m0nka/mcHF/mechanical/back/closer/1.png

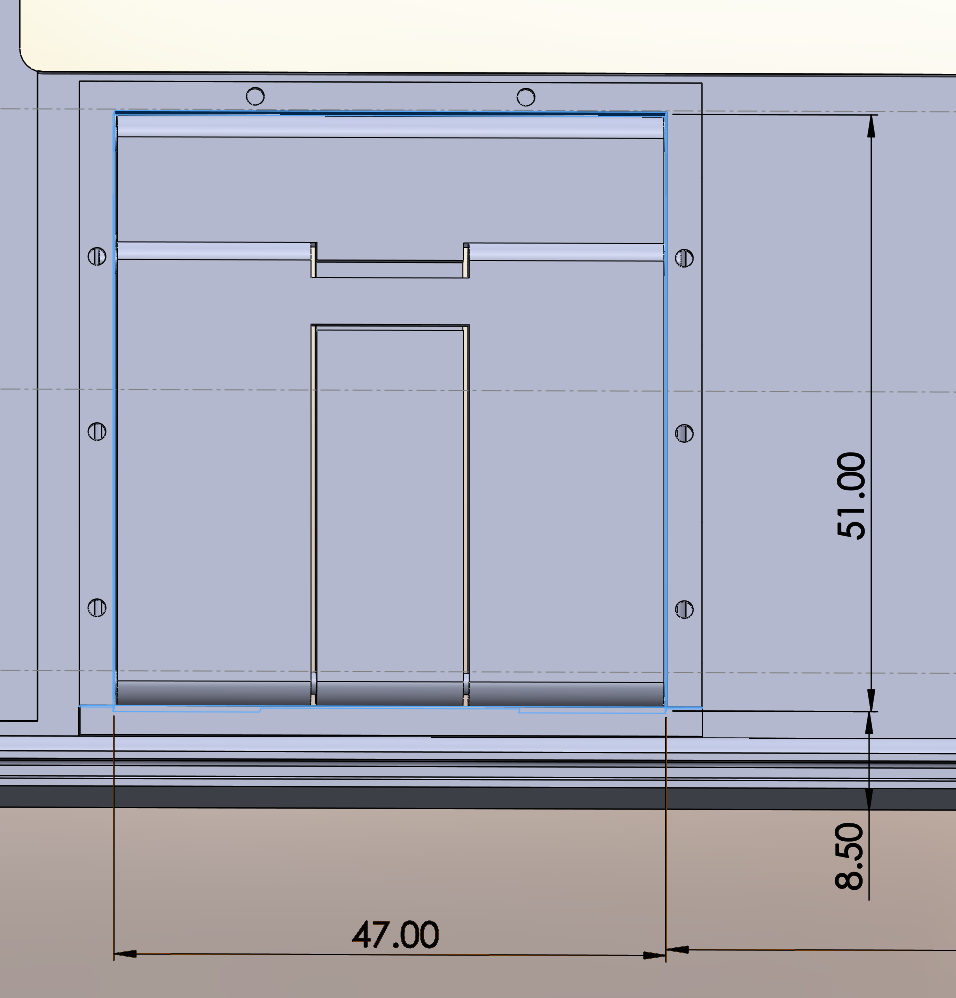
mechanical/back/closer/1.png
