m0nka/mcHF/mechanical/back/closer/2.png

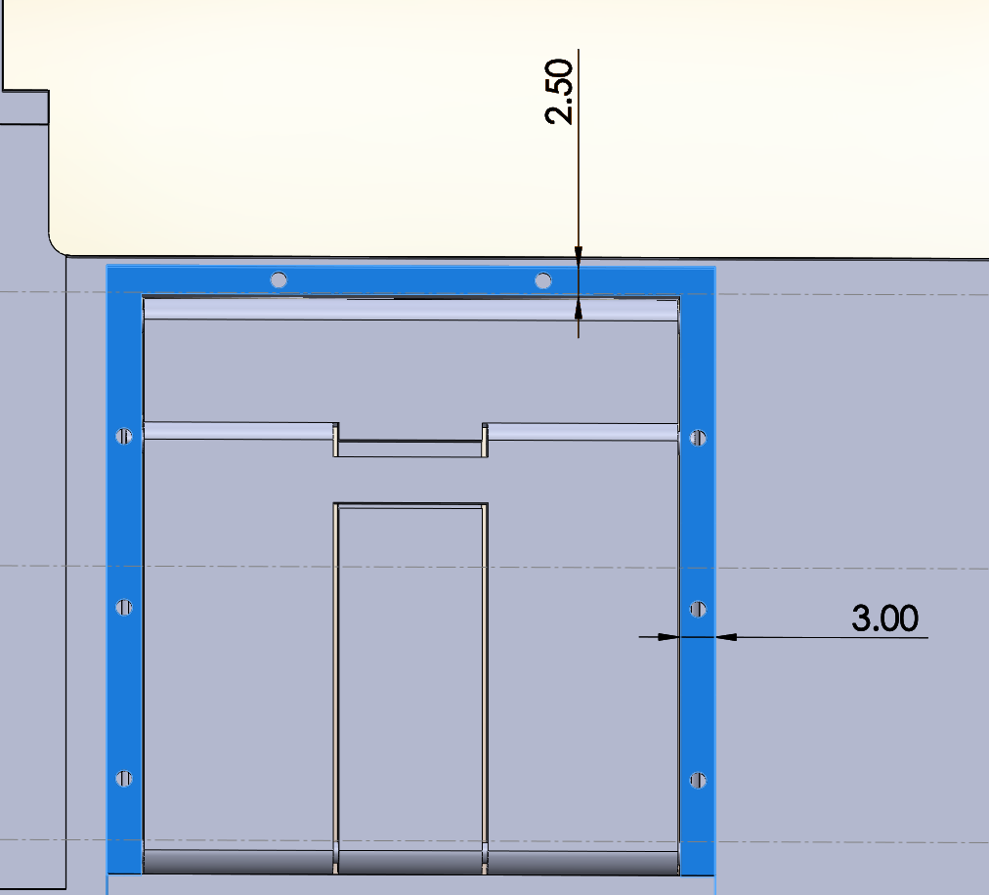
mechanical/back/closer/2.png
