m0nka/mcHF/mechanical/back/closer/3.png

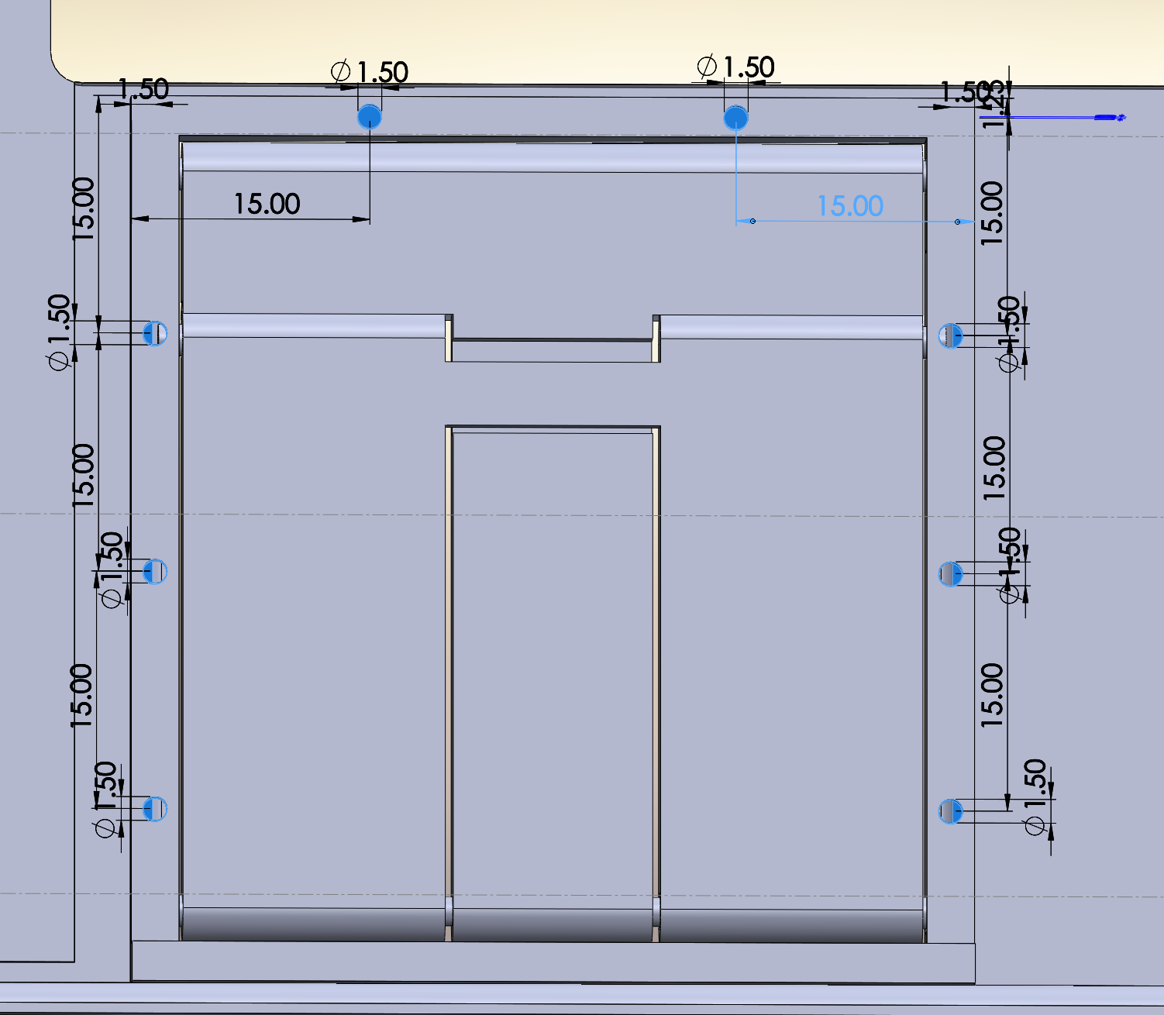
mechanical/back/closer/3.png
