m0nka/mcHF/mechanical/case/AK-C-C19/HTB1J9ANLXXXXXaTXXXXq6xXFXXXU.jpg

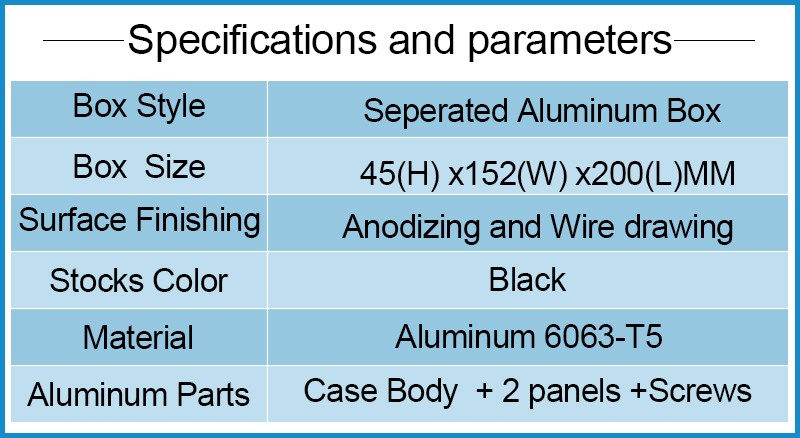
mechanical/case/AK-C-C19/HTB1J9ANLXXXXXaTXXXXq6xXFXXXU.jpg
