m0nka/mcHF/mechanical/case/AK-C-C19/HTB1t6IPLXXXXXXvXXXXq6xXFXXXi.jpg

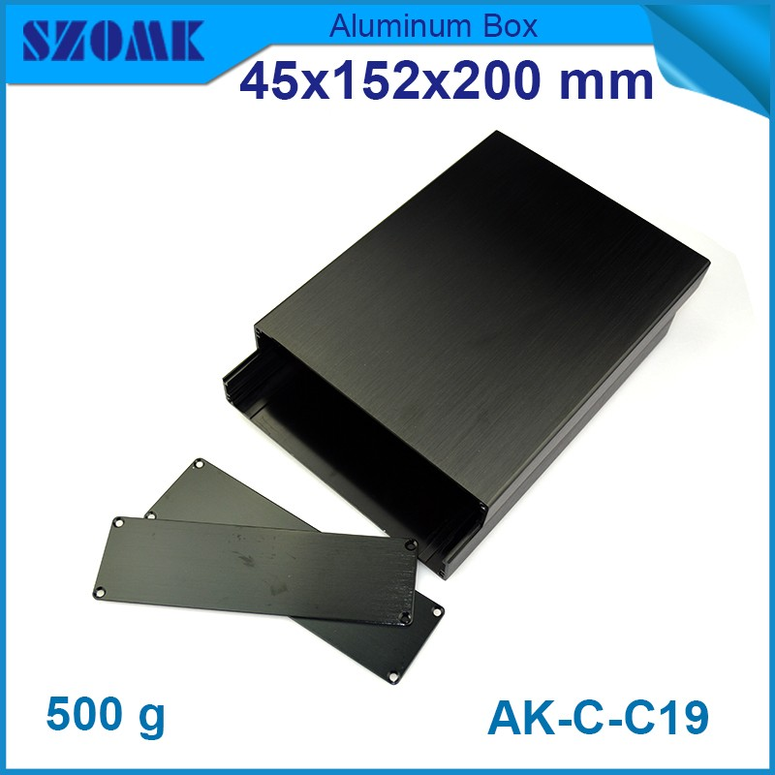
mechanical/case/AK-C-C19/HTB1t6IPLXXXXXXvXXXXq6xXFXXXi.jpg
