m0nka/mcHF/mechanical/case/AK-C-C19/HTB1tHIrLXXXXXaYXVXXq6xXFXXXV.jpg

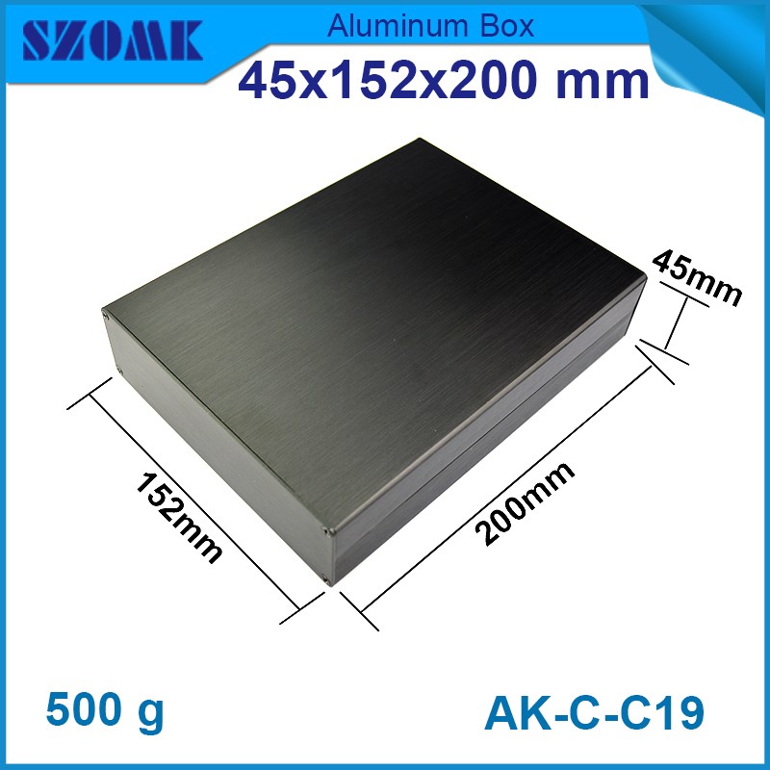
mechanical/case/AK-C-C19/HTB1tHIrLXXXXXaYXVXXq6xXFXXXV.jpg
