m0nka/mcHF/mechanical/case/AK-C-C19/HTB13bgQLXXXXXXDXXXXq6xXFXXXn.jpg

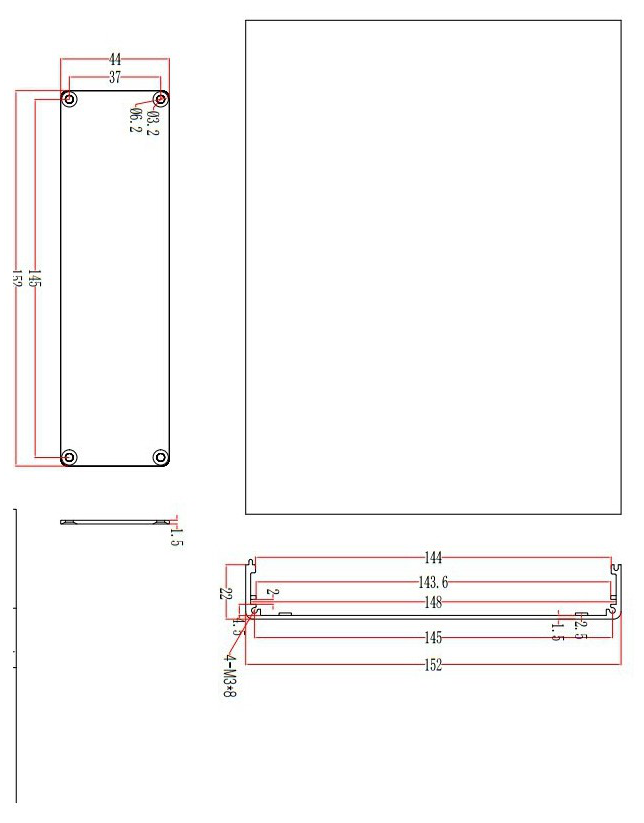
mechanical/case/AK-C-C19/HTB13bgQLXXXXXXDXXXXq6xXFXXXn.jpg
