m0nka/mcHF/testing/gerbers/0_8_5/1.png

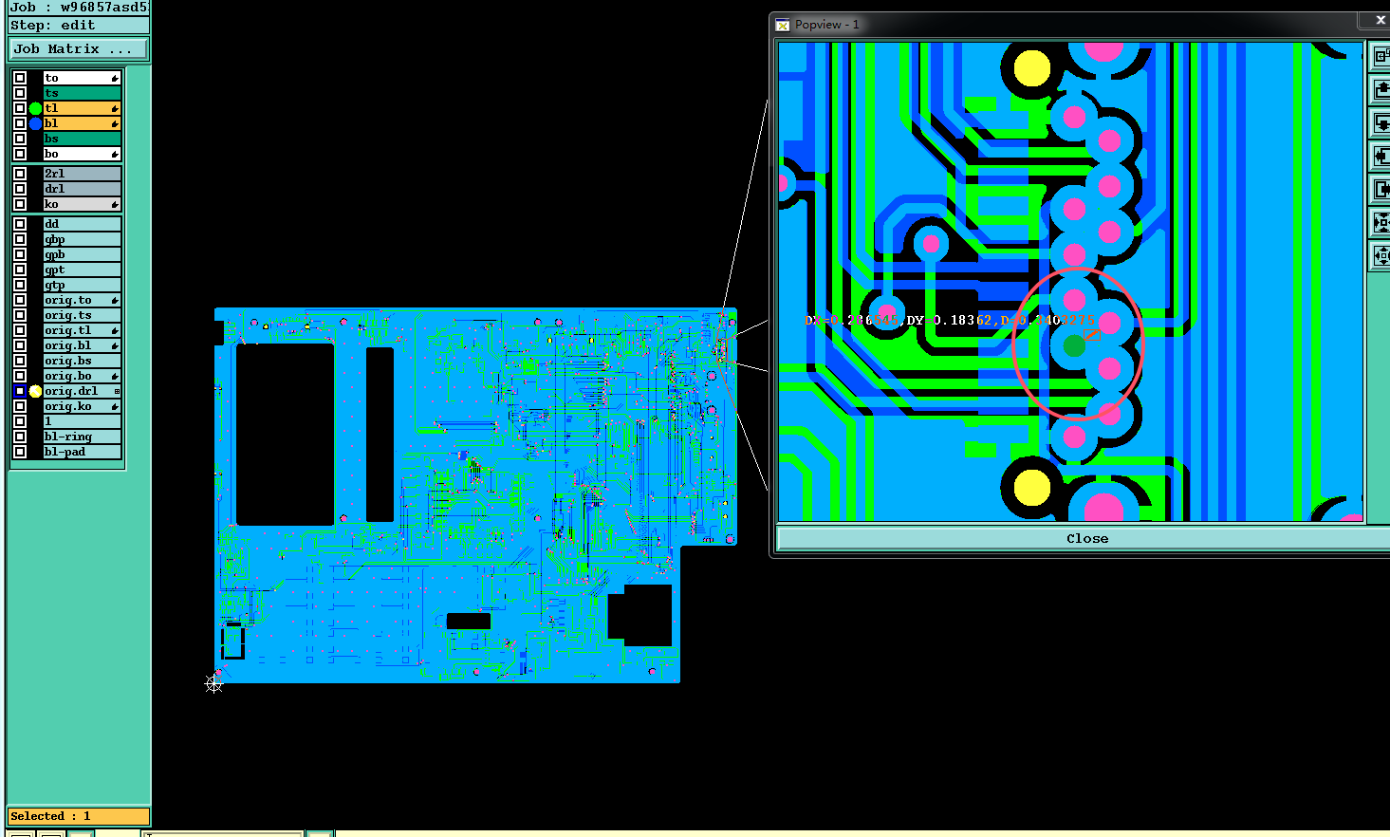
testing/gerbers/0_8_5/1.png
