m0nka/mcHF/firmware/baseband/basesw/mcHF/Inc/main.h

#define HSEM_ID_0           		0 			// CM7 to CM4 Notification
#define HSEM_ID_1           		1 			// CM4 to CM7 Notification
#define BUTTON_PWR_Pin GPIO_PIN_13
#define BUTTON_PWR_GPIO_Port GPIOC
#define PADDLE_DAH_Pin GPIO_PIN_0
#define PADDLE_DAH_GPIO_Port GPIOE
#define PADDLE_DIT_Pin GPIO_PIN_1
#define PADDLE_DIT_GPIO_Port GPIOE
#define TX_LED_PIN              GPIO_PIN_6
#define TX_LED_PIO              GPIOF
