m0nka/mcHF/firmware/app_proc/hw/shared_i2c.c

/************************************************************************************
**                                                                                 **
**                                 mcHF QRP Transceiver                            **
**                         Krassi Atanassov - M0NKA, 2013-2026                     **
**                                                                                 **
**---------------------------------------------------------------------------------**
**                                                                                 **
**  File name:                                                                     **
**  Description:                                                                   **
**  Last Modified:                                                                 **
**  Licence:			https://github.com/m0nka/mcHF/blob/main/LICENSE            **
************************************************************************************/

#include "main.h"
#include "mchf_pro_board.h"

#include "shared_i2c.h"
#include "stm32h747i_discovery_errno.h"

static const I2C_Charac_t I2C_Charac[] =
{
  [I2C_SPEED_FREQ_STANDARD] =
  {
    .freq = 100000,
    .freq_min = 80000,
    .freq_max = 120000,
    .hddat_min = 0,
    .vddat_max = 3450,
    .sudat_min = 250,
    .lscl_min = 4700,
    .hscl_min = 4000,
    .trise = 640,
    .tfall = 20,
    .dnf = I2C_DIGITAL_FILTER_COEF,
  },
  [I2C_SPEED_FREQ_FAST] =
  {
    .freq = 400000,
    .freq_min = 320000,
    .freq_max = 480000,
    .hddat_min = 0,
    .vddat_max = 900,
    .sudat_min = 100,
    .lscl_min = 1300,
    .hscl_min = 600,
    .trise = 250,
    .tfall = 100,
    .dnf = I2C_DIGITAL_FILTER_COEF,
  },
  [I2C_SPEED_FREQ_FAST_PLUS] =
  {
    .freq = 1000000,
    .freq_min = 800000,
    .freq_max = 1200000,
    .hddat_min = 0,
    .vddat_max = 450,
    .sudat_min = 50,
    .lscl_min = 500,
    .hscl_min = 260,
    .trise = 60,
    .tfall = 100,
    .dnf = I2C_DIGITAL_FILTER_COEF,
  },
};

#if (USE_HAL_I2C_REGISTER_CALLBACKS == 1)
static uint32_t IsI2c4MspCbValid = 0;
#endif /* USE_HAL_I2C_REGISTER_CALLBACKS */
static uint32_t I2c1InitCounter = 0;
static I2C_Timings_t I2c_valid_timing[I2C_VALID_TIMING_NBR];
static uint32_t      I2c_valid_timing_nbr = 0;

I2C_HandleTypeDef hbus_i2c1;

SemaphoreHandle_t 	dI2CSemaphore = NULL;

__weak HAL_StatusTypeDef MX_I2C1_Init(I2C_HandleTypeDef *hI2c, uint32_t timing)
{
  HAL_StatusTypeDef status = HAL_OK;

  hI2c->Init.Timing           = timing;
  hI2c->Init.OwnAddress1      = 0;
  hI2c->Init.AddressingMode   = I2C_ADDRESSINGMODE_7BIT;
  hI2c->Init.DualAddressMode  = I2C_DUALADDRESS_DISABLE;
  hI2c->Init.OwnAddress2      = 0;
  hI2c->Init.OwnAddress2Masks = I2C_OA2_NOMASK;
  hI2c->Init.GeneralCallMode  = I2C_GENERALCALL_DISABLE;
  hI2c->Init.NoStretchMode    = I2C_NOSTRETCH_DISABLE;

  if (HAL_I2C_Init(hI2c) != HAL_OK)
  {
    status = HAL_ERROR;
  }
  else
  {
    uint32_t analog_filter;

    analog_filter = I2C_ANALOGFILTER_ENABLE;
    if (HAL_I2CEx_ConfigAnalogFilter(hI2c, analog_filter) != HAL_OK)
    {
      status = HAL_ERROR;
    }
    else
    {
      if (HAL_I2CEx_ConfigDigitalFilter(hI2c, I2C_DIGITAL_FILTER_COEF) != HAL_OK)
      {
        status = HAL_ERROR;
      }
    }
  }

  return status;
}

static void I2C_Compute_PRESC_SCLDEL_SDADEL(uint32_t clock_src_freq, uint32_t I2C_speed)
{
  uint32_t prev_presc = I2C_PRESC_MAX;
  uint32_t ti2cclk;
  int32_t  tsdadel_min, tsdadel_max;
  int32_t  tscldel_min;
  uint32_t presc, scldel, sdadel;
  uint32_t tafdel_min, tafdel_max;

  ti2cclk   = (SEC2NSEC + (clock_src_freq / 2U))/ clock_src_freq;

  tafdel_min = I2C_ANALOG_FILTER_DELAY_MIN;
  tafdel_max = I2C_ANALOG_FILTER_DELAY_MAX;

  /* tDNF = DNF x tI2CCLK
     tPRESC = (PRESC+1) x tI2CCLK
     SDADEL >= {tf +tHD;DAT(min) - tAF(min) - tDNF - [3 x tI2CCLK]} / {tPRESC}
     SDADEL <= {tVD;DAT(max) - tr - tAF(max) - tDNF- [4 x tI2CCLK]} / {tPRESC} */

  tsdadel_min = (int32_t)I2C_Charac[I2C_speed].tfall + (int32_t)I2C_Charac[I2C_speed].hddat_min -
    (int32_t)tafdel_min - (int32_t)(((int32_t)I2C_Charac[I2C_speed].dnf + 3) * (int32_t)ti2cclk);

  tsdadel_max = (int32_t)I2C_Charac[I2C_speed].vddat_max - (int32_t)I2C_Charac[I2C_speed].trise -
    (int32_t)tafdel_max - (int32_t)(((int32_t)I2C_Charac[I2C_speed].dnf + 4) * (int32_t)ti2cclk);


  /* {[tr+ tSU;DAT(min)] / [tPRESC]} - 1 <= SCLDEL */
  tscldel_min = (int32_t)I2C_Charac[I2C_speed].trise + (int32_t)I2C_Charac[I2C_speed].sudat_min;

  if (tsdadel_min <= 0)
  {
    tsdadel_min = 0;
  }

  if (tsdadel_max <= 0)
  {
    tsdadel_max = 0;
  }

  for (presc = 0; presc < I2C_PRESC_MAX; presc++)
  {
    for (scldel = 0; scldel < I2C_SCLDEL_MAX; scldel++)
    {
      /* TSCLDEL = (SCLDEL+1) * (PRESC+1) * TI2CCLK */
      uint32_t tscldel = (scldel + 1U) * (presc + 1U) * ti2cclk;

      if (tscldel >= (uint32_t)tscldel_min)
      {
        for (sdadel = 0; sdadel < I2C_SDADEL_MAX; sdadel++)
        {
          /* TSDADEL = SDADEL * (PRESC+1) * TI2CCLK */
          uint32_t tsdadel = (sdadel * (presc + 1U)) * ti2cclk;

          if ((tsdadel >= (uint32_t)tsdadel_min) && (tsdadel <= (uint32_t)tsdadel_max))
          {
            if(presc != prev_presc)
            {
              I2c_valid_timing[I2c_valid_timing_nbr].presc = presc;
              I2c_valid_timing[I2c_valid_timing_nbr].tscldel = scldel;
              I2c_valid_timing[I2c_valid_timing_nbr].tsdadel = sdadel;
              prev_presc = presc;
              I2c_valid_timing_nbr ++;

              if(I2c_valid_timing_nbr >= I2C_VALID_TIMING_NBR)
              {
                return;
              }
            }
          }
        }
      }
    }
  }
}

static uint32_t I2C_Compute_SCLL_SCLH (uint32_t clock_src_freq, uint32_t I2C_speed)
{
 uint32_t ret = 0xFFFFFFFFU;
  uint32_t ti2cclk;
  uint32_t ti2cspeed;
  uint32_t prev_error;
  uint32_t dnf_delay;
  uint32_t clk_min, clk_max;
  uint32_t scll, sclh;
  uint32_t tafdel_min;

  ti2cclk   = (SEC2NSEC + (clock_src_freq / 2U))/ clock_src_freq;
  ti2cspeed   = (SEC2NSEC + (I2C_Charac[I2C_speed].freq / 2U))/ I2C_Charac[I2C_speed].freq;

  tafdel_min = I2C_ANALOG_FILTER_DELAY_MIN;

  /* tDNF = DNF x tI2CCLK */
  dnf_delay = I2C_Charac[I2C_speed].dnf * ti2cclk;

  clk_max = SEC2NSEC / I2C_Charac[I2C_speed].freq_min;
  clk_min = SEC2NSEC / I2C_Charac[I2C_speed].freq_max;

  prev_error = ti2cspeed;

  for (uint32_t count = 0; count < I2c_valid_timing_nbr; count++)
  {
    /* tPRESC = (PRESC+1) x tI2CCLK*/
    uint32_t tpresc = (I2c_valid_timing[count].presc + 1U) * ti2cclk;

    for (scll = 0; scll < I2C_SCLL_MAX; scll++)
    {
      /* tLOW(min) <= tAF(min) + tDNF + 2 x tI2CCLK + [(SCLL+1) x tPRESC ] */
      uint32_t tscl_l = tafdel_min + dnf_delay + (2U * ti2cclk) + ((scll + 1U) * tpresc);


      /* The I2CCLK period tI2CCLK must respect the following conditions:
      tI2CCLK < (tLOW - tfilters) / 4 and tI2CCLK < tHIGH */
      if ((tscl_l > I2C_Charac[I2C_speed].lscl_min) && (ti2cclk < ((tscl_l - tafdel_min - dnf_delay) / 4U)))
      {
        for (sclh = 0; sclh < I2C_SCLH_MAX; sclh++)
        {
          /* tHIGH(min) <= tAF(min) + tDNF + 2 x tI2CCLK + [(SCLH+1) x tPRESC] */
          uint32_t tscl_h = tafdel_min + dnf_delay + (2U * ti2cclk) + ((sclh + 1U) * tpresc);

          /* tSCL = tf + tLOW + tr + tHIGH */
          uint32_t tscl = tscl_l + tscl_h + I2C_Charac[I2C_speed].trise + I2C_Charac[I2C_speed].tfall;

          if ((tscl >= clk_min) && (tscl <= clk_max) && (tscl_h >= I2C_Charac[I2C_speed].hscl_min) && (ti2cclk < tscl_h))
          {
            int32_t error = (int32_t)tscl - (int32_t)ti2cspeed;

            if (error < 0)
            {
              error = -error;
            }

            /* look for the timings with the lowest clock error */
            if ((uint32_t)error < prev_error)
            {
              prev_error = (uint32_t)error;
              I2c_valid_timing[count].scll = scll;
              I2c_valid_timing[count].sclh = sclh;
              ret = count;
            }
          }
        }
      }
    }
  }

  return ret;
}

static uint32_t I2C_GetTiming(uint32_t clock_src_freq, uint32_t i2c_freq)
{
  uint32_t ret = 0;
  uint32_t speed;
  uint32_t idx;

  if((clock_src_freq != 0U) && (i2c_freq != 0U))
  {
    for ( speed = 0 ; speed <=  (uint32_t)I2C_SPEED_FREQ_FAST_PLUS ; speed++)
    {
      if ((i2c_freq >= I2C_Charac[speed].freq_min) &&
          (i2c_freq <= I2C_Charac[speed].freq_max))
      {
        I2C_Compute_PRESC_SCLDEL_SDADEL(clock_src_freq, speed);
        idx = I2C_Compute_SCLL_SCLH(clock_src_freq, speed);

        if (idx < I2C_VALID_TIMING_NBR)
        {
          ret = ((I2c_valid_timing[idx].presc  & 0x0FU) << 28) |\
                ((I2c_valid_timing[idx].tscldel & 0x0FU) << 20) |\
                ((I2c_valid_timing[idx].tsdadel & 0x0FU) << 16) |\
                ((I2c_valid_timing[idx].sclh & 0xFFU) << 8) |\
                ((I2c_valid_timing[idx].scll & 0xFFU) << 0);
        }
        break;
      }
    }
  }

  return ret;
}

static void I2C1_MspInit(I2C_HandleTypeDef *phi2c)
{
	GPIO_InitTypeDef  gpio_init_structure;
	RCC_PeriphCLKInitTypeDef  RCC_PeriphCLKInitStruct;

	/* Prevent unused argument(s) compilation warning */
	UNUSED(phi2c);

	//printf("shared i2c gpio init\r\n");

	/*** Configure the GPIOs ***/
	/* Enable SCL GPIO clock */
	BUS_I2C1_SCL_GPIO_CLK_ENABLE();

	/* Enable SDA GPIO clock */
	BUS_I2C1_SDA_GPIO_CLK_ENABLE();

	// Use slow clock
	#if 1
	RCC_PeriphCLKInitStruct.PeriphClockSelection = RCC_PERIPHCLK_I2C4;
	RCC_PeriphCLKInitStruct.I2c123ClockSelection = RCC_I2C4CLKSOURCE_CSI;
	HAL_RCCEx_PeriphCLKConfig(&RCC_PeriphCLKInitStruct);
	#endif

	/* Configure I2C Tx as alternate function */
	gpio_init_structure.Pin       = BUS_I2C1_SCL_PIN;
	gpio_init_structure.Mode      = GPIO_MODE_AF_OD;
  	  #ifdef BOARD_EVAL_747
	gpio_init_structure.Pull      = GPIO_NOPULL;
  	  #endif
	#ifdef BOARD_MCHF_PRO
	gpio_init_structure.Pull      = GPIO_PULLUP; // if R48 not installed
	#endif
	gpio_init_structure.Speed     = GPIO_SPEED_FREQ_HIGH;
	gpio_init_structure.Alternate = BUS_I2C1_SCL_AF;
	HAL_GPIO_Init(BUS_I2C1_SCL_GPIO_PORT, &gpio_init_structure);

	/* Configure I2C Rx as alternate function */
	gpio_init_structure.Pin       = BUS_I2C1_SDA_PIN;
	gpio_init_structure.Mode      = GPIO_MODE_AF_OD;
	#ifdef BOARD_EVAL_747
	gpio_init_structure.Pull      = GPIO_NOPULL;
	#endif
	#ifdef BOARD_MCHF_PRO
	gpio_init_structure.Pull      = GPIO_PULLUP; // if R49 not installed
	#endif
	gpio_init_structure.Speed     = GPIO_SPEED_FREQ_HIGH;
	gpio_init_structure.Alternate = BUS_I2C1_SDA_AF;
	HAL_GPIO_Init(BUS_I2C1_SDA_GPIO_PORT, &gpio_init_structure);

	// Configure the I2C peripheral
	BUS_I2C1_CLK_ENABLE();
	BUS_I2C1_FORCE_RESET();
	BUS_I2C1_RELEASE_RESET();
}

static void I2C1_MspDeInit(I2C_HandleTypeDef *phi2c)
{
  GPIO_InitTypeDef  gpio_init_structure;

  /* Prevent unused argument(s) compilation warning */
  UNUSED(phi2c);

  /* Configure I2C Tx, Rx as alternate function */
  gpio_init_structure.Pin = BUS_I2C1_SCL_PIN;
  HAL_GPIO_DeInit(BUS_I2C1_SCL_GPIO_PORT, gpio_init_structure.Pin );
  gpio_init_structure.Pin = BUS_I2C1_SDA_PIN;
  HAL_GPIO_DeInit(BUS_I2C1_SDA_GPIO_PORT, gpio_init_structure.Pin);

  /* Disable I2C clock */
  BUS_I2C1_CLK_DISABLE();
}

static int32_t I2C1_WriteReg(uint16_t DevAddr, uint16_t Reg, uint16_t MemAddSize, uint8_t *pData, uint16_t Length)
{
  if(HAL_I2C_Mem_Write(&hbus_i2c1, DevAddr, Reg, MemAddSize, pData, Length, 1000) == HAL_OK)
  {
    return BSP_ERROR_NONE;
  }

  return BSP_ERROR_BUS_FAILURE;
}

static int32_t I2C1_ReadReg(uint16_t DevAddr, uint16_t Reg, uint16_t MemAddSize, uint8_t *pData, uint16_t Length)
{
  if (HAL_I2C_Mem_Read(&hbus_i2c1, DevAddr, Reg, MemAddSize, pData, Length, 1000) == HAL_OK)
  {
    return BSP_ERROR_NONE;
  }

  return BSP_ERROR_BUS_FAILURE;
}

int32_t shared_i2c_init(void)
{
  int32_t ret = BSP_ERROR_NONE;

  hbus_i2c1.Instance = BUS_I2C1;

  dI2CSemaphore = xSemaphoreCreateMutex();

  if (I2c1InitCounter == 0U)
  {
    I2c1InitCounter++;

    if (HAL_I2C_GetState(&hbus_i2c1) == HAL_I2C_STATE_RESET)
    {
		#if (USE_HAL_I2C_REGISTER_CALLBACKS == 0)
    	/* Init the I2C4 Msp */
    	I2C1_MspInit(&hbus_i2c1);
		#else
    	if (IsI2c4MspCbValid == 0U)
    	{
    		if (BSP_I2C4_RegisterDefaultMspCallbacks() != BSP_ERROR_NONE)
    		{
    			ret = BSP_ERROR_MSP_FAILURE;
    		}
    	}
    	if (ret == BSP_ERROR_NONE)
    	{
		#endif
        if (MX_I2C1_Init(&hbus_i2c1, I2C_GetTiming(HAL_RCC_GetPCLK2Freq(), BUS_I2C1_FREQUENCY)) != HAL_OK)
        {
          ret = BSP_ERROR_BUS_FAILURE;
        }
		#if (USE_HAL_I2C_REGISTER_CALLBACKS == 1)
      }
		#endif
    }
  }

  return ret;
}

//*----------------------------------------------------------------------------
//* Function Name       : shared_i2c_change_pins
//* Object              :
//* Notes    			: PCB rev 0.8.5 has separate pins for codec and bms!
//* Notes   			:
//* Notes    			:
//* Context    			: codec proc or bms
//*----------------------------------------------------------------------------
static void shared_i2c_change_pins(uchar addr)
{
	static uchar 		addr_in_use = 0;
	GPIO_InitTypeDef  	gpio_init_structure;

	if(addr_in_use == addr)
		return;

	//printf("change pins for addr 0x%x\r\n", addr);

	// Disable I2C
	CLEAR_BIT(I2C4->CR1, I2C_CR1_PE);

	if(addr == 0x98)	// codec
	{
		// De-init old
		#ifdef CONTEXT_BMS
		gpio_init_structure.Pin       = BMS_SCL_PIN;
		HAL_GPIO_Init(BMS_SCL_PORT, &gpio_init_structure);
		//
		gpio_init_structure.Pin       = BMS_SDA_PIN;
		HAL_GPIO_Init(BMS_SDA_PORT, &gpio_init_structure);
		#endif

		// As I2C
		gpio_init_structure.Speed     = GPIO_SPEED_FREQ_HIGH;
		gpio_init_structure.Mode      = GPIO_MODE_AF_OD;

		gpio_init_structure.Pin       = BUS_I2C1_SCL_PIN;
		gpio_init_structure.Alternate = BUS_I2C1_SCL_AF;
		HAL_GPIO_Init(BUS_I2C1_SCL_GPIO_PORT, &gpio_init_structure);
		//
		gpio_init_structure.Pin       = BUS_I2C1_SDA_PIN;
		gpio_init_structure.Alternate = BUS_I2C1_SDA_AF;
		HAL_GPIO_Init(BUS_I2C1_SDA_GPIO_PORT, &gpio_init_structure);
	}
	else	// bms
	{
		// De-init old
		gpio_init_structure.Pin       = BUS_I2C1_SCL_PIN;
		HAL_GPIO_Init(BUS_I2C1_SCL_GPIO_PORT, &gpio_init_structure);
		//
		gpio_init_structure.Pin       = BUS_I2C1_SDA_PIN;
		HAL_GPIO_Init(BUS_I2C1_SDA_GPIO_PORT, &gpio_init_structure);

		// As I2C
		gpio_init_structure.Speed     = GPIO_SPEED_FREQ_HIGH;
		gpio_init_structure.Mode      = GPIO_MODE_AF_OD;

		gpio_init_structure.Pin       = BMS_SCL_PIN;
		gpio_init_structure.Alternate = GPIO_AF4_I2C4;
		HAL_GPIO_Init(BMS_SCL_PORT, &gpio_init_structure);

		gpio_init_structure.Pin       = BMS_SDA_PIN;
		gpio_init_structure.Alternate = GPIO_AF4_I2C4;
		HAL_GPIO_Init(BMS_SDA_PORT, &gpio_init_structure);
	}

	// Enable I2C
	SET_BIT(I2C4->CR1, I2C_CR1_PE);

	addr_in_use = addr;
}

//
// ToDo: Do we need to call before power off ?
//
int32_t shared_i2c_deinit(void)
{
  int32_t ret  = BSP_ERROR_NONE;

  I2c1InitCounter--;
  if (I2c1InitCounter == 0U)
  {
	#if (USE_HAL_I2C_REGISTER_CALLBACKS == 0)
    I2C1_MspDeInit(&hbus_i2c1);
	#endif /* (USE_HAL_I2C_REGISTER_CALLBACKS == 0) */

    /* Init the I2C */
    if (HAL_I2C_DeInit(&hbus_i2c1) != HAL_OK)
    {
      ret = BSP_ERROR_BUS_FAILURE;
    }
  }

  // ToDo: Delete semaphore on cleanup ?

  return ret;
}

int32_t shared_i2c_write_reg(uint16_t DevAddr, uint16_t Reg, uint8_t *pData, uint16_t Length)
{
	int32_t ret;

	if(dI2CSemaphore == NULL)
		return BSP_ERROR_PERIPH_FAILURE;

	if(xSemaphoreTake(dI2CSemaphore, (TickType_t)0) != pdTRUE)
		return BSP_ERROR_PERIPH_FAILURE;

	shared_i2c_change_pins(DevAddr);

	if(I2C1_WriteReg(DevAddr, Reg, I2C_MEMADD_SIZE_8BIT, pData, Length) == 0)
	{
		ret = BSP_ERROR_NONE;
	}
	else
	{
		if( HAL_I2C_GetError(&hbus_i2c1) == HAL_I2C_ERROR_AF)
		{
			ret = BSP_ERROR_BUS_ACKNOWLEDGE_FAILURE;
		}
		else
		{
			ret =  BSP_ERROR_PERIPH_FAILURE;
		}
	}

	xSemaphoreGive(dI2CSemaphore);
	return ret;
}

int32_t shared_i2c_read_reg(uint16_t DevAddr, uint16_t Reg, uint8_t *pData, uint16_t Length)
{
	int32_t ret;

	if(dI2CSemaphore == NULL)
		return BSP_ERROR_PERIPH_FAILURE;

	if(xSemaphoreTake(dI2CSemaphore, (TickType_t)0) != pdTRUE)
	{
		//printf( "unable to claim shared i2c %s \r\n", pcTaskGetName(NULL));
		return BSP_ERROR_PERIPH_FAILURE;
	}

	shared_i2c_change_pins(DevAddr);

	//printf( "shared i2c read from %s \r\n", pcTaskGetName(NULL));

	if(I2C1_ReadReg(DevAddr, Reg, I2C_MEMADD_SIZE_8BIT, pData, Length) == 0)
	{
		ret = BSP_ERROR_NONE;
	}
	else
	{
		if( HAL_I2C_GetError(&hbus_i2c1) == HAL_I2C_ERROR_AF)
		{
			ret = BSP_ERROR_BUS_ACKNOWLEDGE_FAILURE;
		}
		else
		{
			ret =  BSP_ERROR_PERIPH_FAILURE;
		}
	}

	xSemaphoreGive(dI2CSemaphore);
	return ret;
}

#if 1
int32_t shared_i2c_is_ready(uint16_t DevAddr, uint32_t Trials)
{
	int32_t ret = BSP_ERROR_NONE;

	if(dI2CSemaphore == NULL)
		return BSP_ERROR_PERIPH_FAILURE;

	if(xSemaphoreTake(dI2CSemaphore, (TickType_t)50) != pdTRUE)
		return BSP_ERROR_PERIPH_FAILURE;

	shared_i2c_change_pins(DevAddr);

	if(HAL_I2C_IsDeviceReady(&hbus_i2c1, DevAddr, Trials, 1000) != HAL_OK)
	{
		ret = BSP_ERROR_BUSY;
	}

	xSemaphoreGive(dI2CSemaphore);
	return ret;
}
#endif

#if 0

int32_t BSP_I2C1_WriteReg16(uint16_t DevAddr, uint16_t Reg, uint8_t *pData, uint16_t Length)
{
  int32_t ret;

  if(I2C1_WriteReg(DevAddr, Reg, I2C_MEMADD_SIZE_16BIT, pData, Length) == 0)
  {
    ret = BSP_ERROR_NONE;
  }
  else
  {
    if( HAL_I2C_GetError(&hbus_i2c1) == HAL_I2C_ERROR_AF)
    {
      ret = BSP_ERROR_BUS_ACKNOWLEDGE_FAILURE;
    }
    else
    {
      ret =  BSP_ERROR_PERIPH_FAILURE;
    }
  }

  return ret;
}
#endif
#if 0

int32_t BSP_I2C1_ReadReg16(uint16_t DevAddr, uint16_t Reg, uint8_t *pData, uint16_t Length)
{
  int32_t ret;

  if(I2C1_ReadReg(DevAddr, Reg, I2C_MEMADD_SIZE_16BIT, pData, Length) == 0)
  {
    ret = BSP_ERROR_NONE;
  }
  else
  {
    if( HAL_I2C_GetError(&hbus_i2c1) == HAL_I2C_ERROR_AF)
    {
      ret = BSP_ERROR_BUS_ACKNOWLEDGE_FAILURE;
    }
    else
    {
      ret =  BSP_ERROR_PERIPH_FAILURE;
    }
  }

  return ret;
}
#endif

#if 0
/**
  * @brief  Delay function
  * @retval Tick value
  */
int32_t BSP_GetTick(void)
{
  return (int32_t)HAL_GetTick();
}
#endif

#if (USE_HAL_I2C_REGISTER_CALLBACKS == 1)
/**
  * @brief Register Default I2C4 Bus Msp Callbacks
  * @retval BSP status
  */
int32_t BSP_I2C1_RegisterDefaultMspCallbacks (void)
{
  int32_t ret = BSP_ERROR_NONE;

  __HAL_I2C_RESET_HANDLE_STATE(&hbus_i2c1);

  /* Register default MspInit/MspDeInit Callback */
  if(HAL_I2C_RegisterCallback(&hbus_i2c1, HAL_I2C_MSPINIT_CB_ID, I2C4_MspInit) != HAL_OK)
  {
    ret = BSP_ERROR_PERIPH_FAILURE;
  }
  else if(HAL_I2C_RegisterCallback(&hbus_i2c1, HAL_I2C_MSPDEINIT_CB_ID, I2C4_MspDeInit) != HAL_OK)
  {
    ret = BSP_ERROR_PERIPH_FAILURE;
  }
  else
  {
    IsI2c4MspCbValid = 1U;
  }

  /* BSP status */
  return ret;
}

/**
  * @brief Register I2C4 Bus Msp Callback registering
  * @param Callbacks     pointer to I2C4 MspInit/MspDeInit callback functions
  * @retval BSP status
  */
int32_t BSP_I2C1_RegisterMspCallbacks (BSP_I2C_Cb_t *Callback)
{
  int32_t ret = BSP_ERROR_NONE;

  __HAL_I2C_RESET_HANDLE_STATE(&hbus_i2c1);

  /* Register MspInit/MspDeInit Callbacks */
  if(HAL_I2C_RegisterCallback(&hbus_i2c1, HAL_I2C_MSPINIT_CB_ID, Callback->pMspI2cInitCb) != HAL_OK)
  {
    ret = BSP_ERROR_PERIPH_FAILURE;
  }
  else if(HAL_I2C_RegisterCallback(&hbus_i2c1, HAL_I2C_MSPDEINIT_CB_ID, Callback->pMspI2cDeInitCb) != HAL_OK)
  {
    ret = BSP_ERROR_PERIPH_FAILURE;
  }
  else
  {
    IsI2c4MspCbValid = 1U;
  }

  /* BSP status */
  return ret;
}
#endif /* USE_HAL_I2C_REGISTER_CALLBACKS */
